yunjieshi/ya36/images/2.jpg

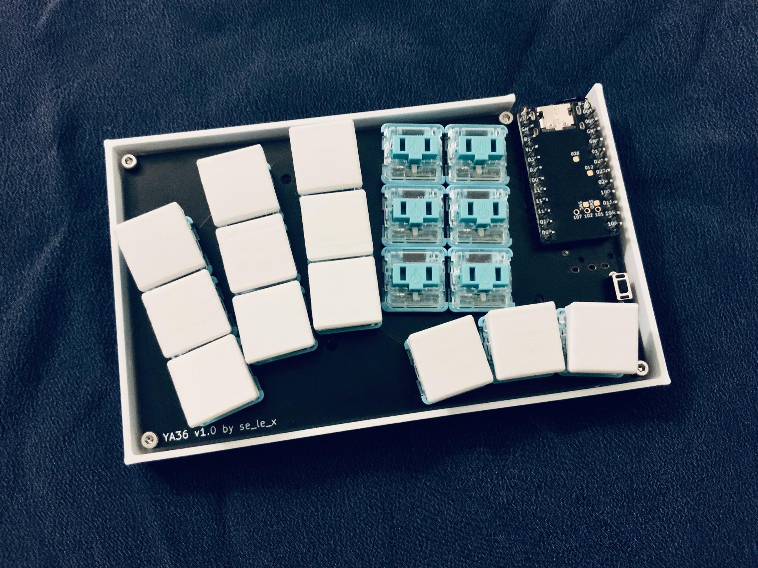
images/2.jpg
